lisasnt/Position-and-Temperature-Controller/media/adc channel config.png

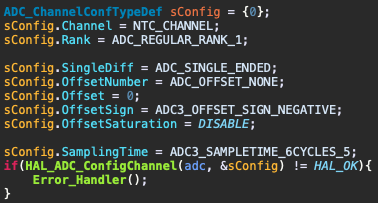
media/adc channel config.png
