lisasnt/Position-and-Temperature-Controller/media/bit mask.png

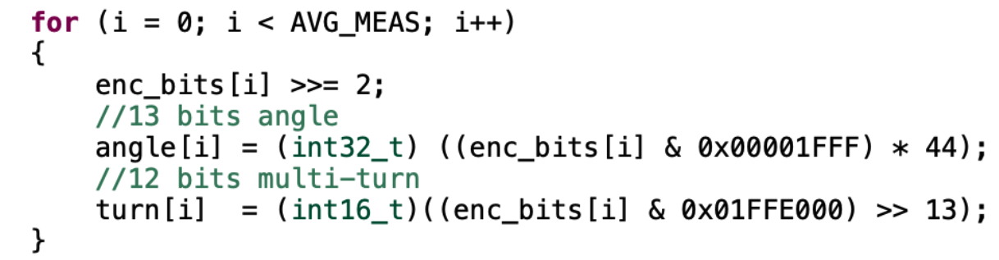
media/bit mask.png
