lisasnt/Position-and-Temperature-Controller/media/circuito di condizionamento PTC e NTC.png

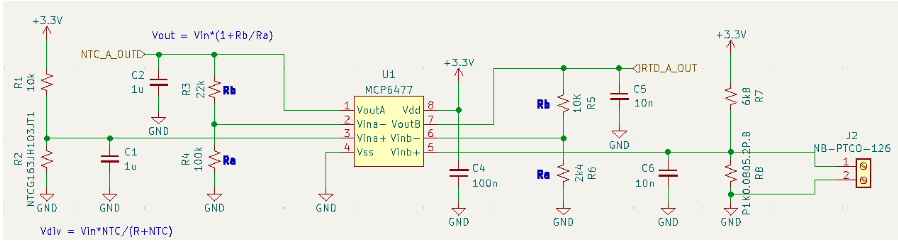
media/circuito di condizionamento PTC e NTC.png
