lisasnt/Position-and-Temperature-Controller/media/connectors.png

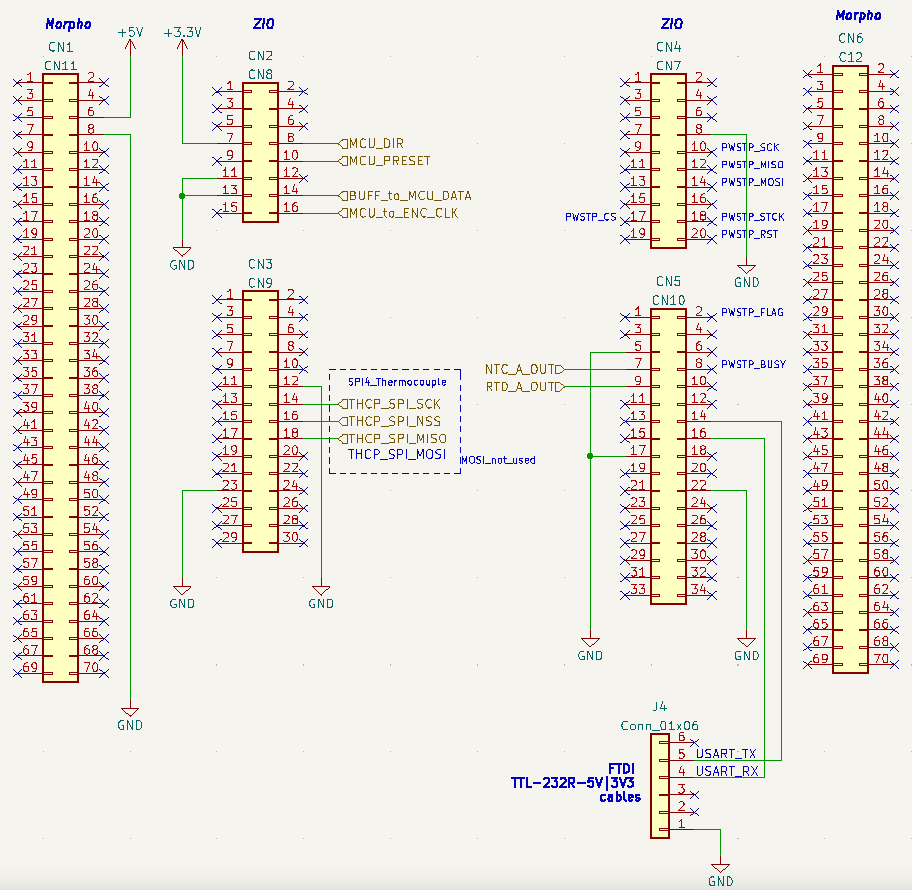
media/connectors.png
