lisasnt/Position-and-Temperature-Controller/media/connettore encoder.png

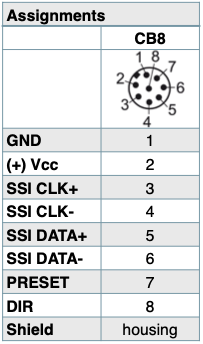
media/connettore encoder.png
