lisasnt/Position-and-Temperature-Controller/media/encoder trasmission.png

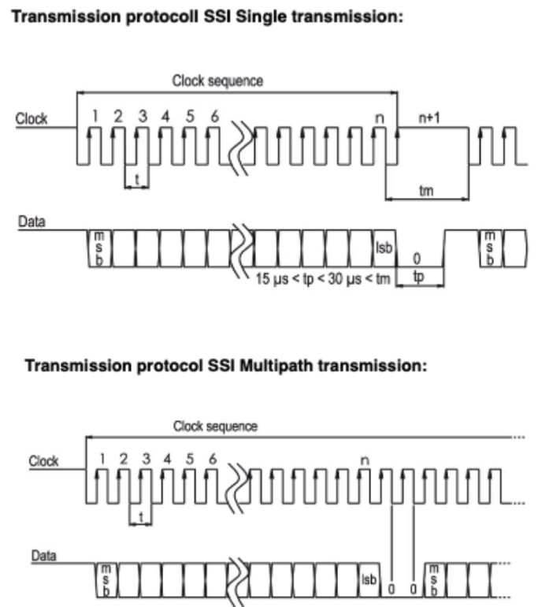
media/encoder trasmission.png
