lisasnt/Position-and-Temperature-Controller/media/ioc.png

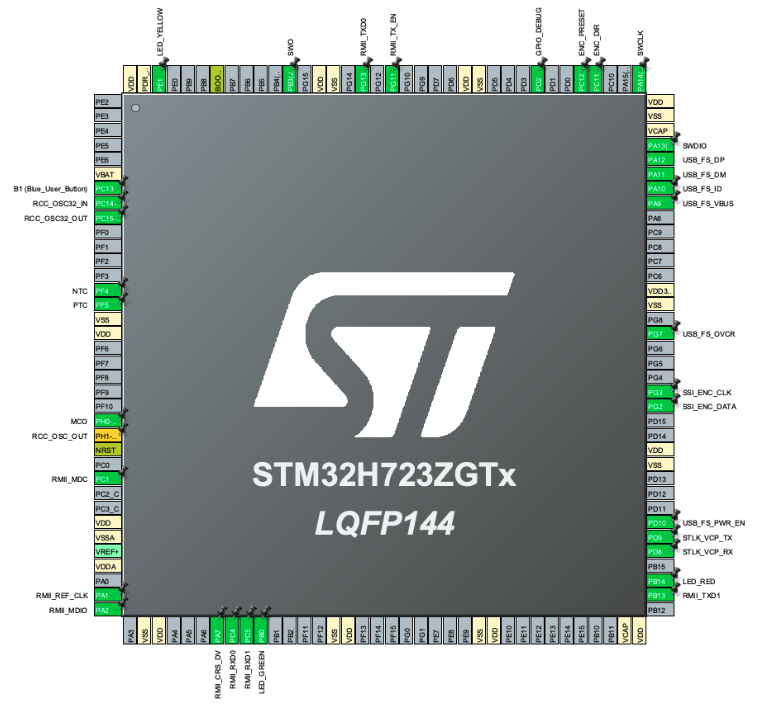
media/ioc.png
