lisasnt/Position-and-Temperature-Controller/media/Schema top e bottom.png

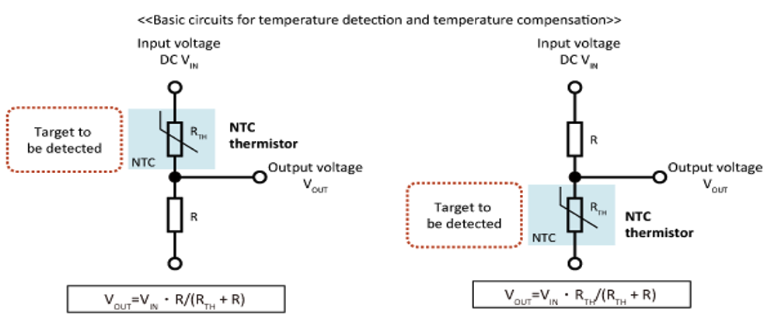
media/Schema top e bottom.png
