lisasnt/Position-and-Temperature-Controller/media/stmBoard.jpg

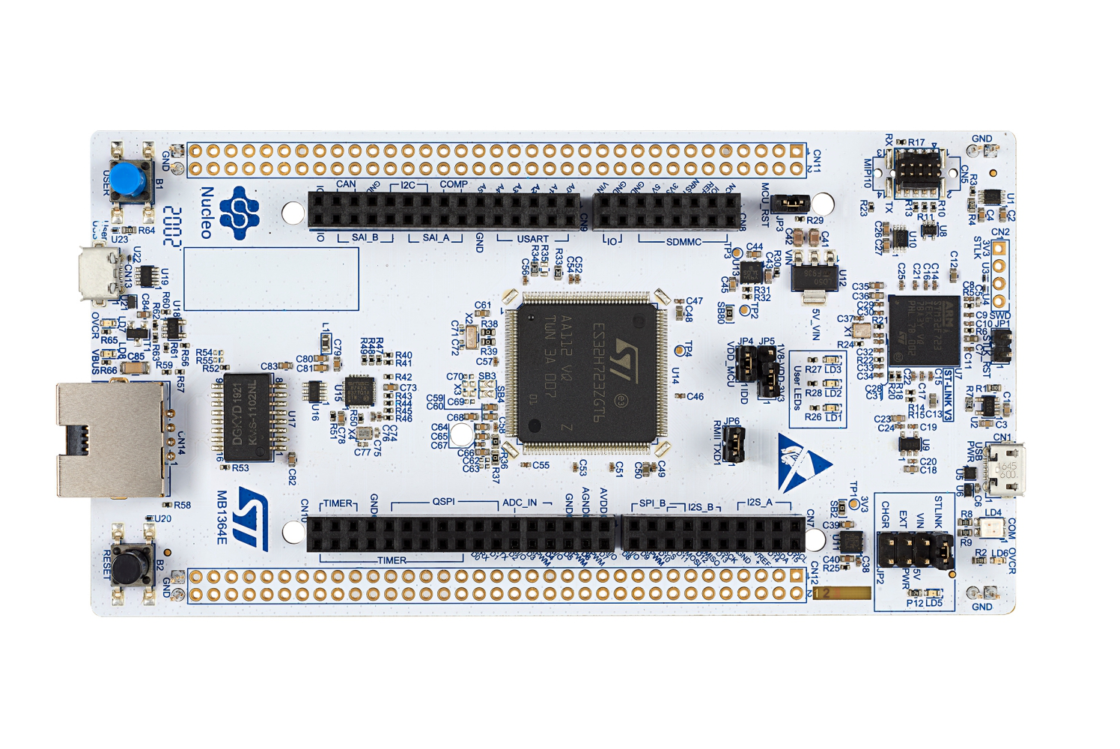
media/stmBoard.jpg
