lisasnt/Position-and-Temperature-Controller/media/uart_1.png

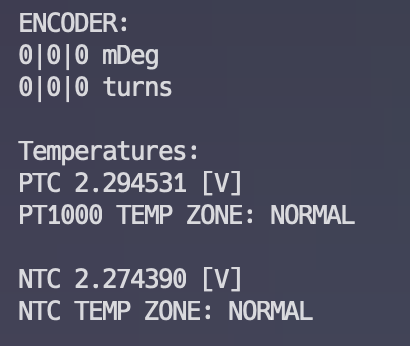
media/uart_1.png
