lisasnt/Position-and-Temperature-Controller/media/uart_2.png

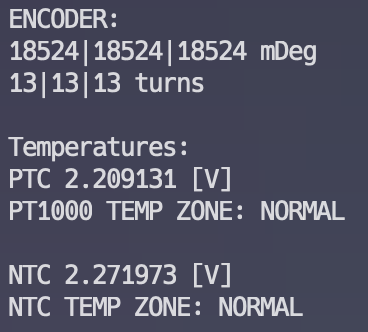
media/uart_2.png
